RajHarsor/Mouse-Push-Pull-Lever-Task/Behavioral Code/Working Code/Arduino IDE Versions/RigBehaviorBoxCode/CoordinateCodePushPull/CoordinateCodePushPull.ino

//Pins
#define REST_PIN 33
#define PUSH_PIN 34
#define PULL_PIN 35
#define LED_PIN 0
#define LICK_BNC 1
#define X_COORD A0
#define Y_COORD A1

//Threshold values
int PUSH; // Set the push threshold value to a value greater than the REST_UPPERBOUND value
int PULL; // Set the pull threshold value to a value less than the REST_LOWERBOUND value
int REST_LOWERBOUND;
int REST_UPPERBOUND;


unsigned int x; // Variable to store the value read from the X axis of the Joystick
unsigned int y; // Variable to store the value read from the Y axis of the Joystick
unsigned long long timestamp = millis(); // Variable to store the time at which the values were read


// Lick Sensor Stuffs
#include <Wire.h>
#include "Adafruit_MPR121.h"

#ifndef _BV
#define _BV(bit) (1 << (bit))
#endif

Adafruit_MPR121 cap = Adafruit_MPR121();
uint16_t currtouched = 0;
int i = 0;

//
void writePins(int pin) // Function to set all pins to low at the beginning of each loop
{
  for(int i=REST_PIN; i<=PULL_PIN; i++)
  {
    if(i == pin)
    {
      digitalWrite(i, HIGH);
    }
    else
    {
      digitalWrite(i, LOW);
    }
  }
}

void parseInput() {
  Serial.println("Enter the PUSH threshold, PULL threshold, REST LOWERBOUND threshold, and the REST UPPERBOUND threshold seperated by commas - PUSH, PULL, REST LOWERBOUND, REST UPPERBOUND (e.g. '520, 490, 500, 510')");
  Serial.println("ENTER VALUES HERE AFTER INPUTTING ISI DELAY VALUES");

  while (!Serial.available()) {

  }

  String input = Serial.readStringUntil('\n');
  int numValues = sscanf(input.c_str(), "%d, %d, %d, %d", &PUSH, &PULL, &REST_LOWERBOUND, &REST_UPPERBOUND);

  if (numValues == 4) {
    Serial.println("Successfully input thresholds!");
  } else {
    Serial.println("Invalid input. Please enter the values again");
  }
  }

void setup() {

  Serial.begin(115200);
  pinMode(REST_PIN, OUTPUT); // Sets the Rest pin as an output, tells the Behavior Teensy that when the arm is in the rest position
  pinMode(PUSH_PIN, OUTPUT); // Sets the Push pin as an output, tells the Behavior Teensy that when the arm is in the push position
  pinMode(PULL_PIN, OUTPUT); // Sets the Pull pin as an output, tells the Behavior Teensy that when the arm is in the pull position
  pinMode(LED_PIN, OUTPUT); // Sets the LED pin as an output is lit when the mouse is in the rest position
  pinMode(LICK_BNC, OUTPUT);
  while (!Serial) {
    delay (50);
  if (!cap.begin(0x5A)) {
    Serial.println("MPR121 not found, check wiring?");
  }
  }
  parseInput();
}

void loop() {
  timestamp = millis(); // Stores the time at which the values were read
  x = map(analogRead(A0), 0, 1023, 1023, 0);; // Replace with the pin connected to the joystick X axis
  y = analogRead(A1); // Replace with the pin connected to the joystick Y axis

  Serial.print(x); // Prints the X value
  Serial.print(" , ");
  Serial.print(y); // Prints the Y value
  Serial.print(" , ");
  Serial.print(timestamp); // Prints the time at which the values were read in microseconds
  Serial.print(" , ");

  if(x >= REST_LOWERBOUND && x <= REST_UPPERBOUND)
  {
    writePins(REST_PIN);
    digitalWrite(LED_PIN, HIGH);
  }
  else if(x >= PUSH)
  {
    writePins(PUSH_PIN);;
    digitalWrite(LED_PIN, LOW);

  }
  else if(x <= PULL)
  {
    writePins(PULL_PIN);
    digitalWrite(LED_PIN, LOW);
  }

  if(digitalRead(29) == HIGH)
  {
    Serial.print("Stage 1: Rest ,");
  }
  else if(digitalRead(30) == HIGH)
  {
    Serial.print("Stage 2: Push/Pull ,");
  }
  else if (digitalRead(31) == HIGH) {
    Serial.print("Stage 3: Water Retrival ,");
  }
  else if (digitalRead(32) == HIGH) {
    Serial.print("Stage 4: ISI ,");
  }
  else 
  {
    Serial.print("None ;");
  }
  currtouched = cap.touched();
  if ((currtouched & _BV(1))){
    digitalWrite(LICK_BNC, HIGH);
    Serial.println(" Lick ;");
  } else {
    digitalWrite(LICK_BNC, LOW);
    Serial.println(" No Lick ;");
  }
  delay(1);
}
