RajHarsor/Mouse-Push-Pull-Lever-Task/Behavioral Code/Working Code/Arduino IDE Versions/RigBehaviorBoxCode/BehaviorCodeRig/hold_time_mod_visual.cpp

#include "parse_scripts.h"
#include "hold_time_mod_visual.h"

void holdTimeVisualTask() {
    switch (visualStage) {
        case 1:
        case 2:
            break;
        case 3:
            break;
        case 4:
            break;
    }
        }
