RajHarsor/Mouse-Push-Pull-Lever-Task/Behavioral Code/Working Code/Arduino IDE Versions/RigBehaviorBoxCode/BehaviorCodeRig/isi_delay_mod_visual.cpp

#include "isi_delay_mod_visual.h"

void isiDelayModVisual() {
    switch (visualStage) {
            case 1:
                break;
            case 2: case 3: case 4:
                break;
        }
    }
