RajHarsor/Mouse-Push-Pull-Lever-Task/Behavioral Code/Working Code/Arduino IDE Versions/RigBehaviorBoxCode/BehaviorCodeRig/reaction_time_mod_visual.cpp

#include "reaction_time_mod_visual.h"

void reactionTimeWindowModVisual() {
    switch (visualStage){
        case 1: case 2: case 4:
            break;
        case 3:
            if (timeOutTime > 1000 && correct == true) {
            timeOutTime = timeOutTime - 10;
            }
            break;
        }
}
