RajHarsor/Mouse-Push-Pull-Lever-Task/Behavioral Code/Working Code/Arduino IDE Versions/RigBehaviorBoxCode/BehaviorCodeRig/solenoid_open_time.h

#ifndef SOLENOID_OPEN_TIME_H
#define SOLENOID_OPEN_TIME_H

extern int decision;
extern int positionA;
extern int positionB;
extern int OpenTime;
extern int ArrayCount1;
extern int ArrayCount2;

#include <Arduino.h>

void solenoidOpenTime();

#endif
